mon/TataconUSB/Software/Tataconfig/tatacon.png

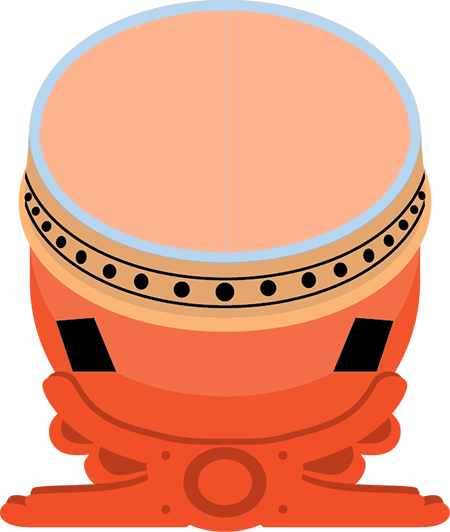
Software/Tataconfig/tatacon.png
