mon/TataconUSB/Hardware/Case/TataCase_V5_Thin.scad

include <TataCase_V5_Thin_Base.scad>

rotate([90,0,0])
board();
