mon/TataconUSB/Hardware/Case/TataCase_V5_Thin_Base.scad

include <TataconCaseBase.scad>

usb_relative_z = 0;
board_thickness = 0.8;
board_clearance_bottom = 1.8;
