mon/TataconUSB/Hardware/Case/TataCase_V5_Thin_Rear.scad

include <TataCase_V5_Thin_Base.scad>

rear_clip();
